stephenholtz/phonotaxis-experiments/config/seraph_speaker_config.png

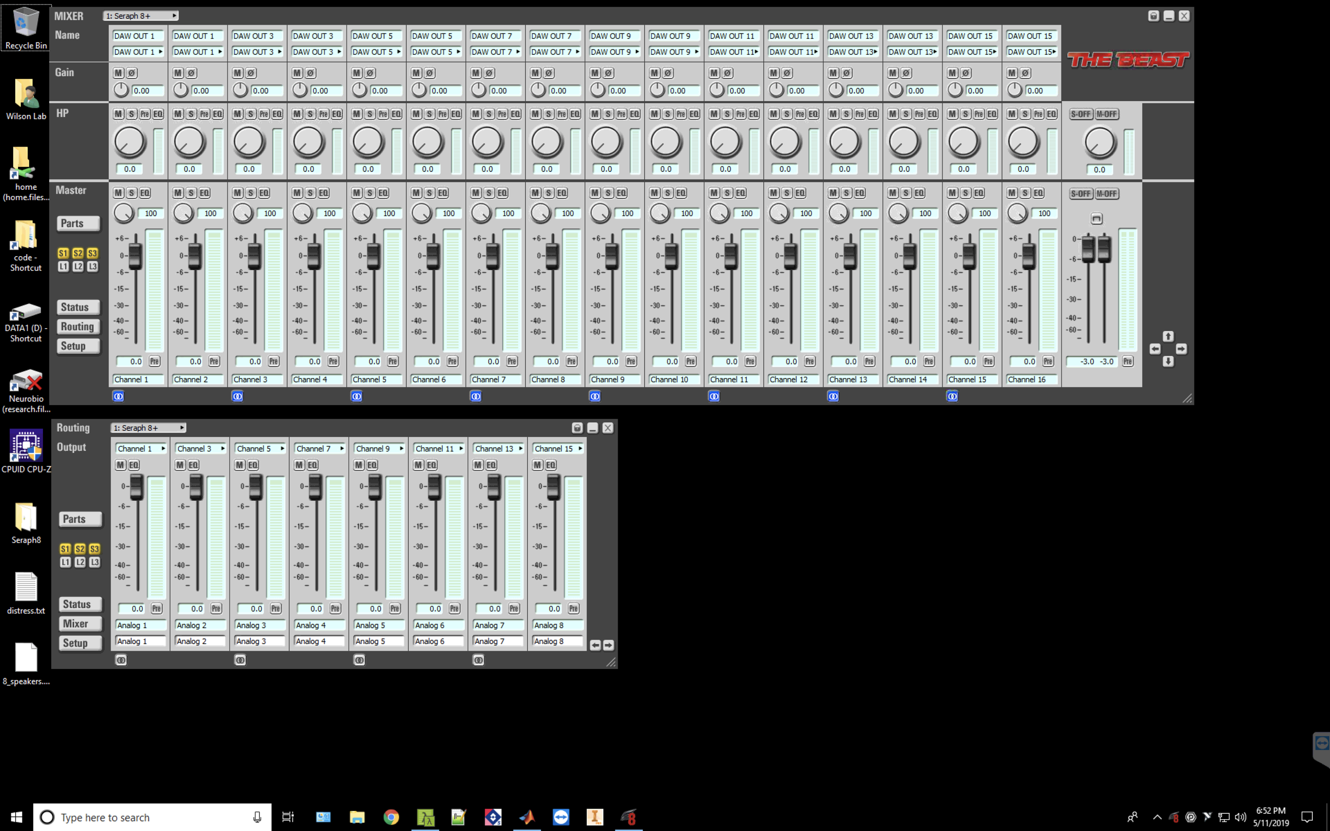
config/seraph_speaker_config.png
