stephenholtz/phonotaxis-experiments/literature/Screenshot 2019-05-11 21.53.13.png

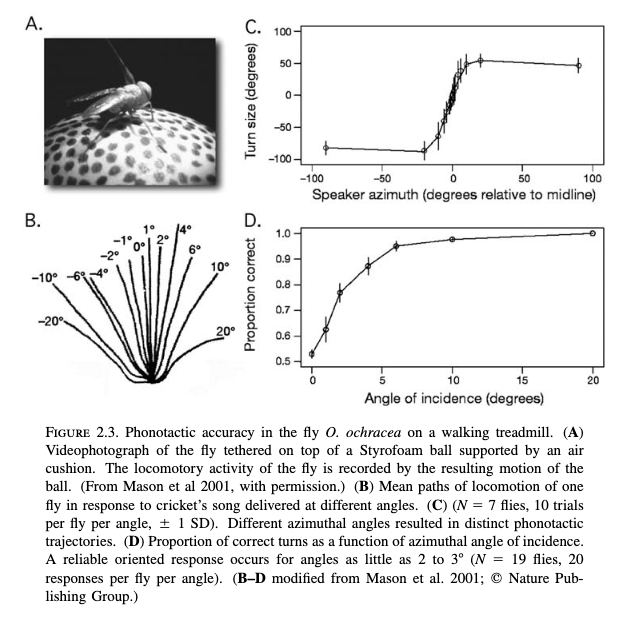
literature/Screenshot 2019-05-11 21.53.13.png
