stephenholtz/phonotaxis-experiments/design-files/ball-assembly/ball-assembly-just-holder-ball-face-wireframe.png

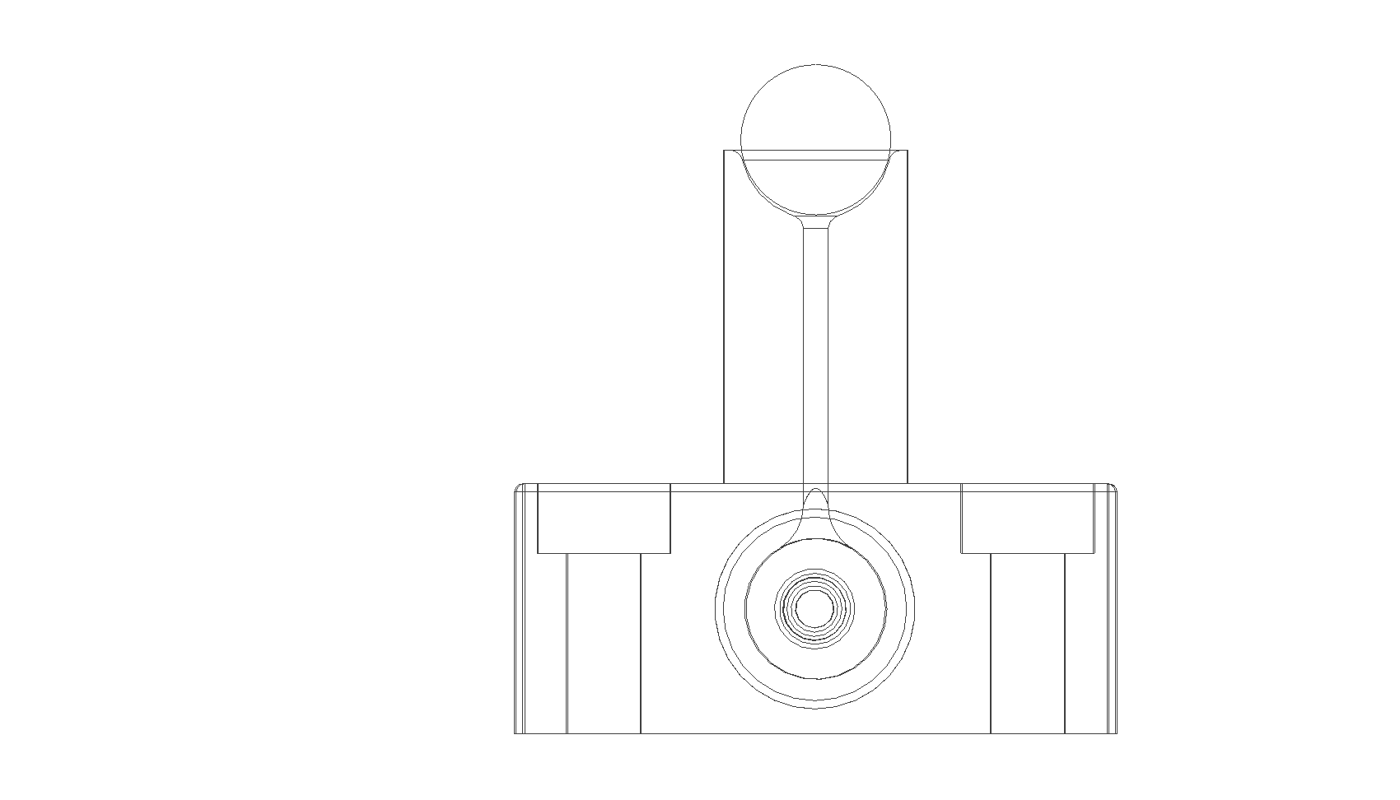
design-files/ball-assembly/ball-assembly-just-holder-ball-face-wireframe.png
