stephenholtz/phonotaxis-experiments/design-files/ball-assembly/ball-assembly-just-holder-ball-profile-wireframe.png

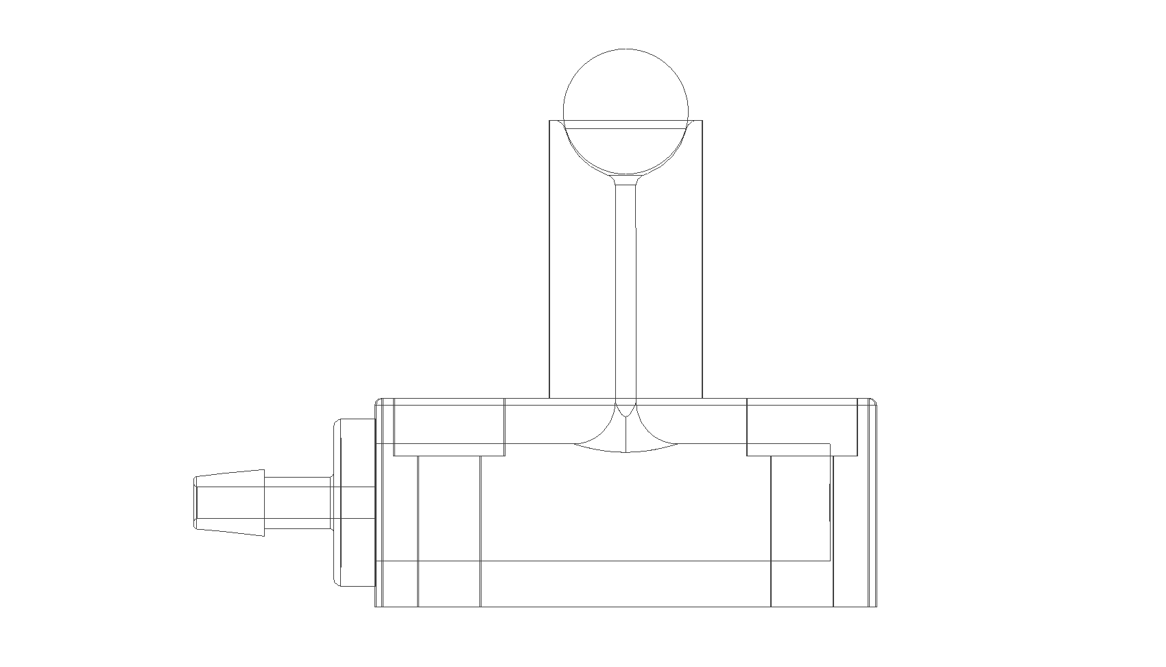
design-files/ball-assembly/ball-assembly-just-holder-ball-profile-wireframe.png
