stephenholtz/phonotaxis-experiments/design-files/ball-assembly/ball-assembly-just-holder-ball.png

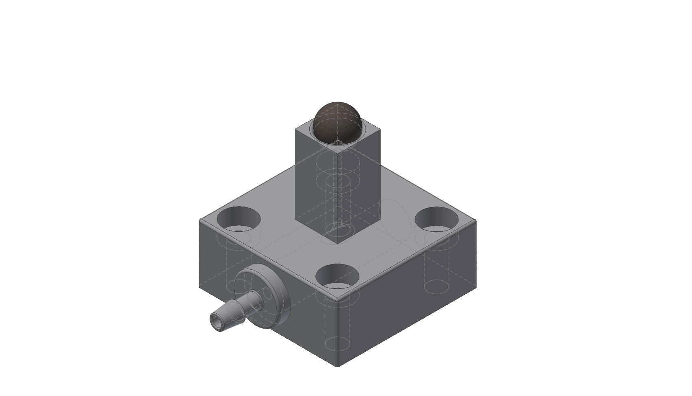
design-files/ball-assembly/ball-assembly-just-holder-ball.png
