stephenholtz/phonotaxis-experiments/design-files/speaker-assembly/speaker_assembly_v2.png

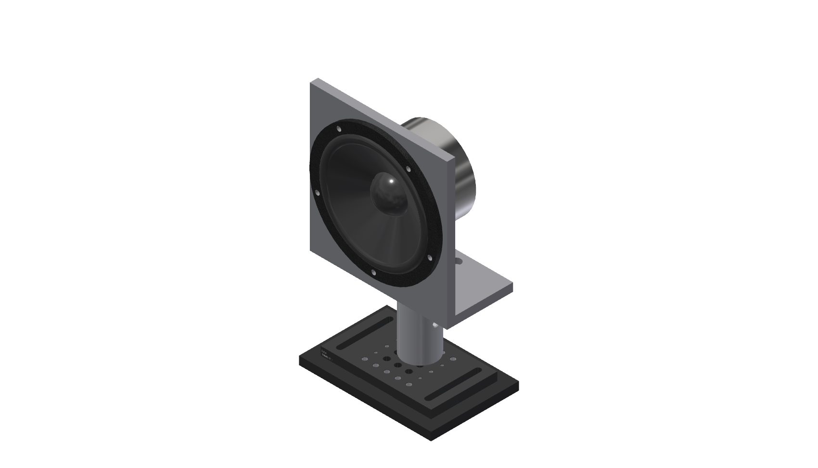
design-files/speaker-assembly/speaker_assembly_v2.png
