stephenholtz/phonotaxis-experiments/design-files/turntable-breadboard-assembly/turntable-breadboard-assembly.png

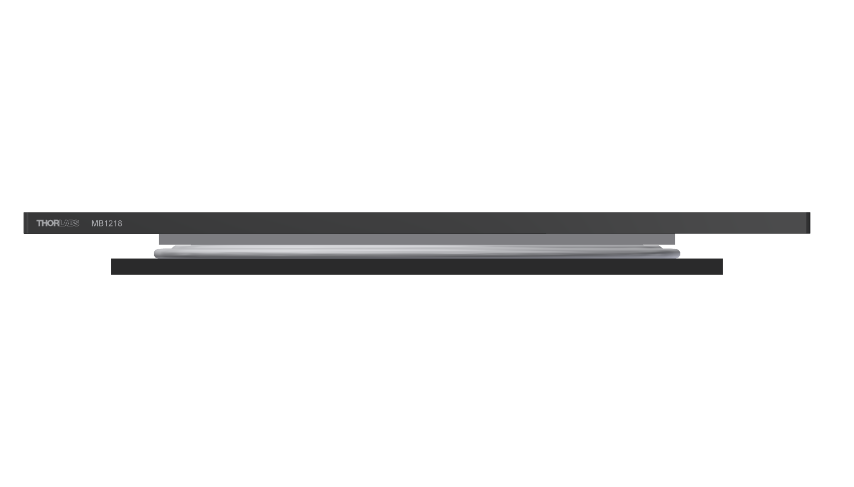
design-files/turntable-breadboard-assembly/turntable-breadboard-assembly.png
