stephenholtz/phonotaxis-experiments/design-files/vr-opto-assembly/vr-opto-assembly-rearleft.png

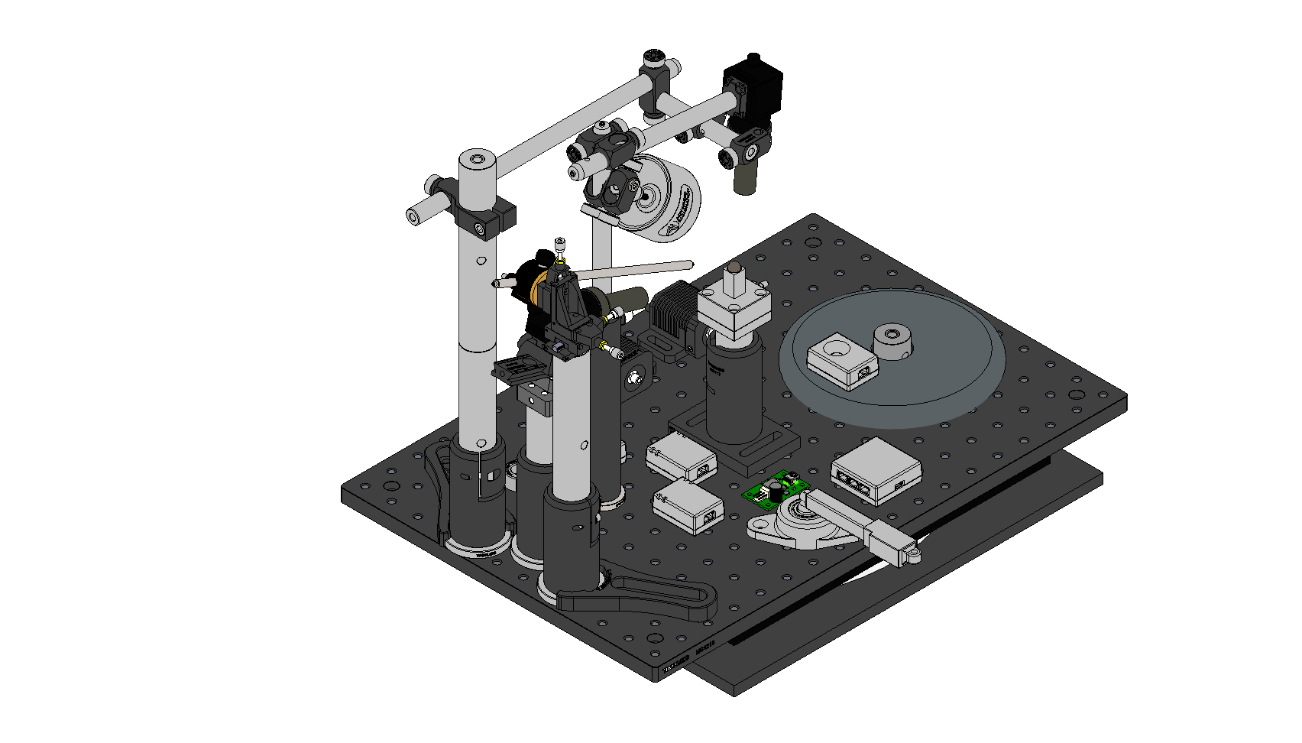
design-files/vr-opto-assembly/vr-opto-assembly-rearleft.png
