stephenholtz/phonotaxis-experiments/design-files/vr-opto-assembly/vr-opto-assembly.png

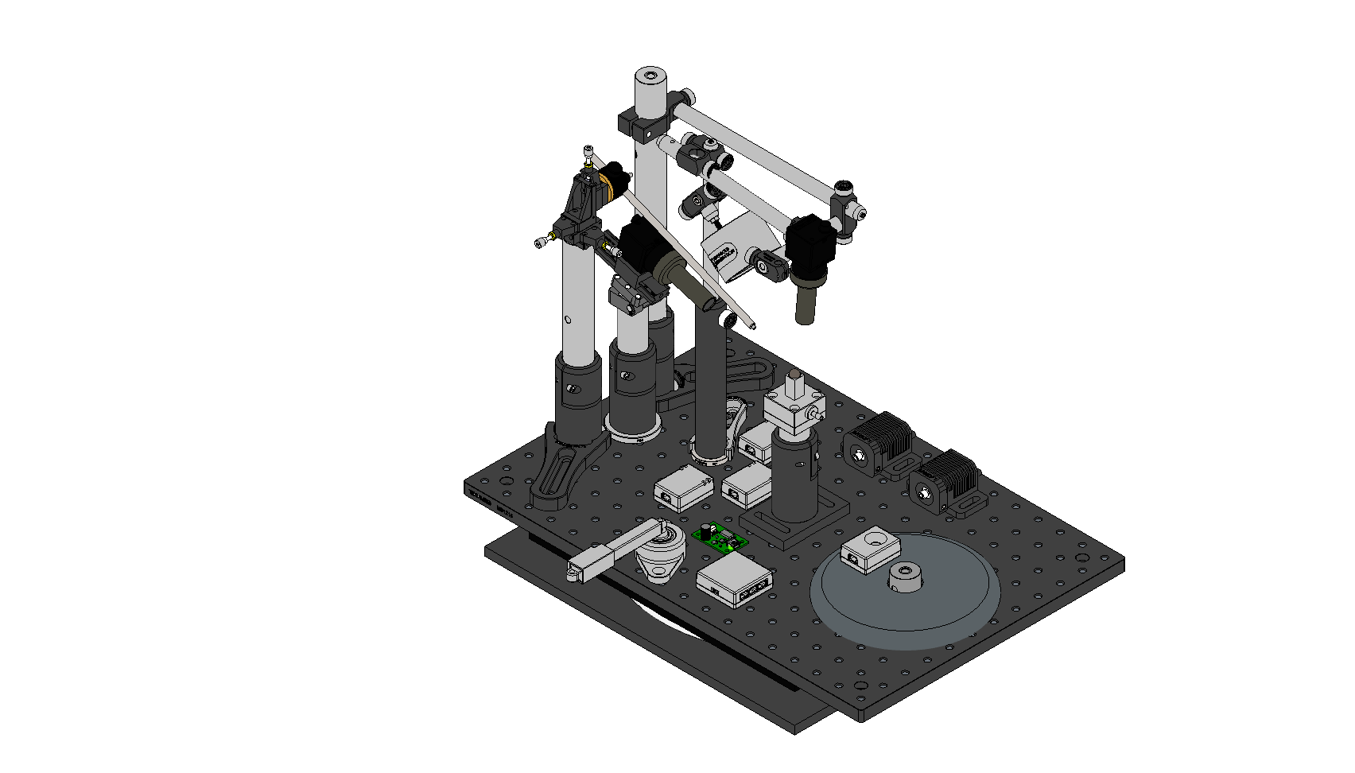
design-files/vr-opto-assembly/vr-opto-assembly.png
